hugokernel/RaspiOMix/doc/io.png

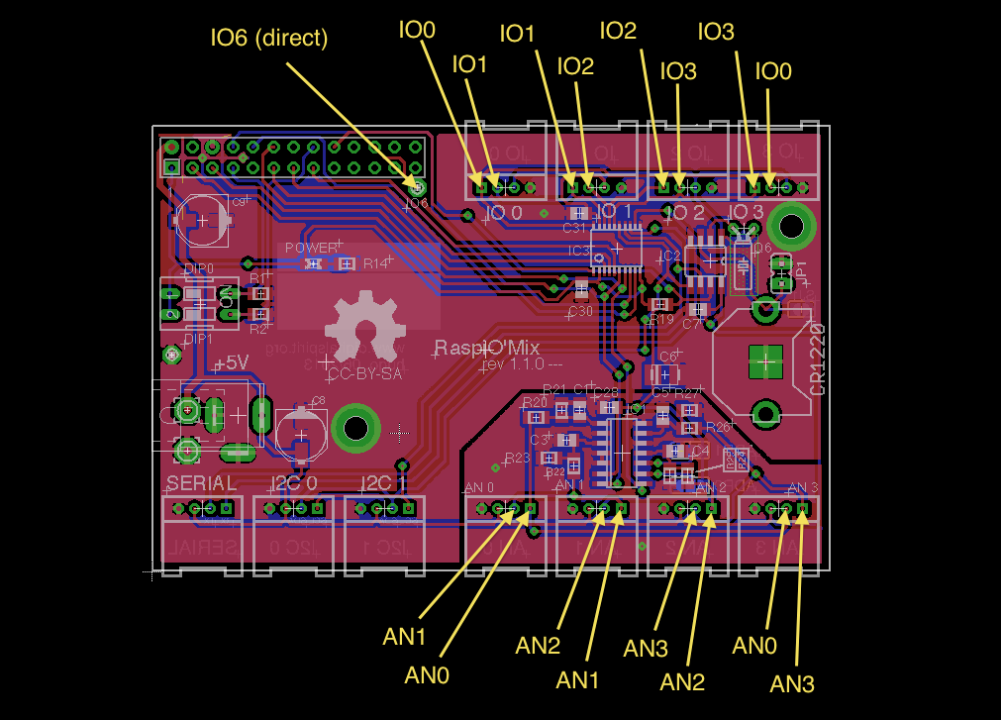
doc/io.png
