hugokernel/RaspiOMix/export/1.0.0/images/pcb.png

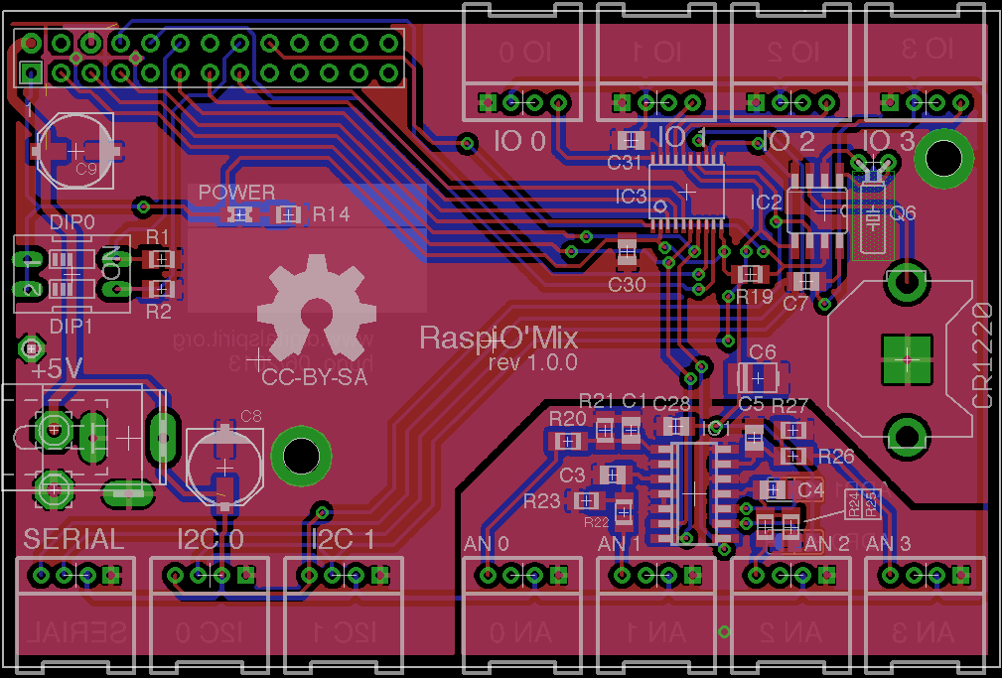
export/1.0.0/images/pcb.png
