hugokernel/RaspiOMix/export/1.1.1/images/schema.png

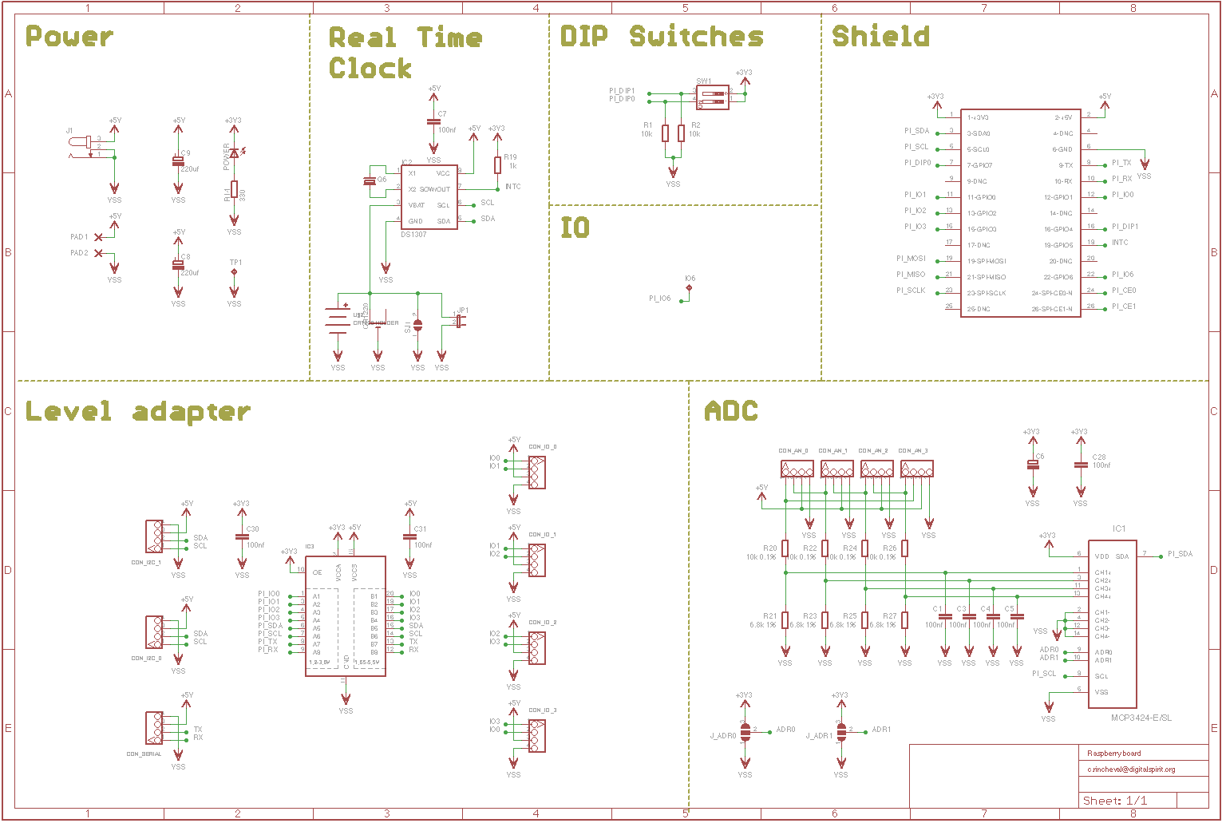
export/1.1.1/images/schema.png
