hugokernel/RaspiOMix/export/2.0.0/images/pcb.png

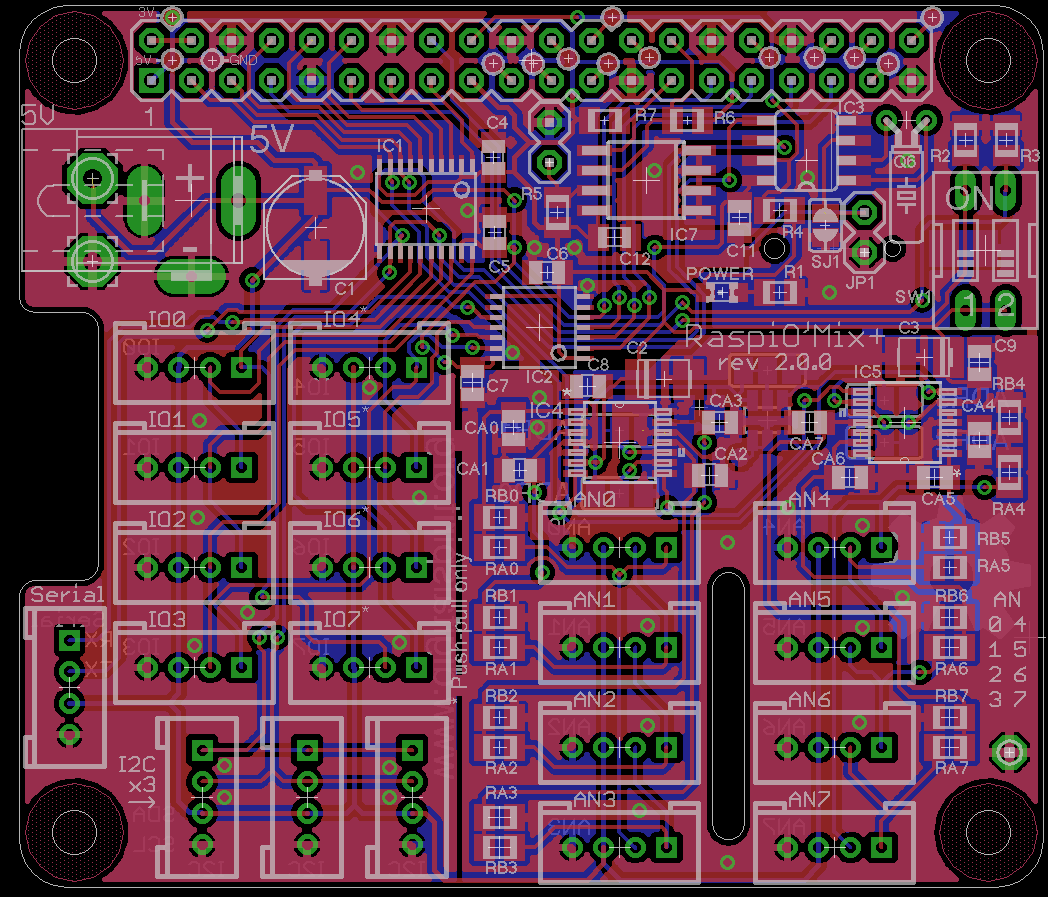
export/2.0.0/images/pcb.png
